Gvico/AT-Blaster/Code/Application/C Files/Globals.c

/*****************************************************
HERE SHOULD BE PLACED GLOBAL PROJECT VARIABLES.
DON'T FORGET TO DECLARE VARIABLES AS EXTERNAL IN 
GLOBALS.H
*****************************************************/

#include "../Headers/Globals.h"

volatile char rx_string[8];
volatile char rx_i = 0;

char game_on = 1;
int points_i = 0;
char points_a[5];
