Gvico/AT-Blaster/Code/Application/Headers/Globals.h

/*****************************************************
HERE SHOULD BE PLACED GLOBAL PROJECT VARIABLES AS 
EXTERNAL FROM GLOBALS.C
*****************************************************/

#ifndef GLOBALS_H
#define GLOBALS_H

extern volatile char rx_string[8];
extern volatile char rx_i;

extern char game_on;
extern int points_i;
extern char points_a[5];

#endif
