Gvico/AT-Blaster/Code/Application/Headers/Lasergame.h

/*
 * Lasergame.h
 *
 * Created: 21-05-21 18:42:03
 *  Author: Gilles
 */ 


#ifndef LASERGAME_H_
#define LASERGAME_H_


extern void pistol_hit(void);
extern void pistol_shoot(void);
extern void pistol_endgame(void);


#endif /* LASERGAME_H_ */
